PhobGCC/PhobGCC-SW/PhobGCC/common/stick.h

#ifndef STICKCAL_H
#define STICKCAL_H

#include <cmath>

#include "curveFitting.h"
#include "structsAndEnums.h"
#include "filter.h"

//TODO: either put these const globals in varables.h or make them #defines
//origin values, useful for writing readable stick positions
const int _intOrigin = 127;
const float _floatOrigin = 127.5;

//////values used for calibration
const int _noOfNotches = 16;
const int _noOfCalibrationPoints = _noOfNotches * 2;
const int _noOfAdjNotches = 12;
const int _fitOrder = 3; //fit order used in the linearization step
const float _maxStickAngle = 0.4886921906;//28 degrees; this is the max angular deflection of the stick.

const float _defaultCalPoints[_noOfCalibrationPoints] =  {
	0.0,0.0,//right
	0.0,0.0,
	0.0,0.0,//up right
	0.0,0.0,
	0.0,0.0,//up
	0.0,0.0,
	0.0,0.0,//up left
	0.0,0.0,
	0.0,0.0,//left
	0.0,0.0,
	0.0,0.0,//down left
	0.0,0.0,
	0.0,0.0,//down
	0.0,0.0,
	0.0,0.0,//down right
	0.0,0.0};

//Defaults
//                                                         right        notch 1      up right     notch 2      up           notch 3      up left      notch 4      left         notch 5      down left    notch 6      down         notch 7      down right   notch 8
//                                                         0            1            2            3            4            5            6            7            8            9            10           11           12           13           14           15
const int _calOrder[_noOfCalibrationPoints] =             {0, 1,        8, 9,       16, 17,       24, 25,      4, 5,        12, 13,      20, 21,      28, 29,      2, 3,        6, 7,        10, 11,      14, 15,      18, 19,      22, 23,      26, 27,      30, 31};
const float _notchAngleDefaults[_noOfNotches] =           {0,           M_PI/8.0,    M_PI*2/8.0,  M_PI*3/8.0,  M_PI*4/8.0,  M_PI*5/8.0,  M_PI*6/8.0,  M_PI*7/8.0,  M_PI*8/8.0,  M_PI*9/8.0,  M_PI*10/8.0, M_PI*11/8.0, M_PI*12/8.0, M_PI*13/8.0, M_PI*14/8.0, M_PI*15/8.0};
const NotchStatus _notchStatusDefaults[_noOfNotches] =    {CARDINAL,    TERT_ACTIVE, SECONDARY,   TERT_ACTIVE, CARDINAL,    TERT_ACTIVE, SECONDARY,   TERT_ACTIVE, CARDINAL,    TERT_ACTIVE, SECONDARY,   TERT_ACTIVE, CARDINAL,    TERT_ACTIVE, SECONDARY,   TERT_ACTIVE};
//                                                         up right     up left      down left    down right   notch 1      notch 2      notch 3      notch 4      notch 5      notch 6      notch 7      notch 8
const int _notchAdjOrder[_noOfAdjNotches] =               {2,           6,           10,          14,          1,           3,           5,           7,           9,           11,          13,          15};

float linearize(const float point, const float coefficients[]){
	return (coefficients[0]*(point*point*point) + coefficients[1]*(point*point) + coefficients[2]*point + coefficients[3]);
};

/*
 * calcStickValues computes the stick x/y coordinates from angle.
 * This requires weird trig because the stick moves spherically.
 */
void calcStickValues(float angle, float* x, float* y){
	*x = 100*atan2f((sinf(_maxStickAngle)*cosf(angle)),cosf(_maxStickAngle))/_maxStickAngle;
	*y = 100*atan2f((sinf(_maxStickAngle)*sinf(angle)),cosf(_maxStickAngle))/_maxStickAngle;
};

/*
 * Convert the x/y coordinates (actually angles on a sphere) to an azimuth
 * We first convert to a 3D coordinate and then drop to 2D, then arctan it
 * This does the opposite of calcStickValues, ideally.
 */
void angleOnSphere(const float x, const float y, float& angle){
	float xx = sinf(x*_maxStickAngle/100) * cosf(y*_maxStickAngle/100);
	float yy = cosf(x*_maxStickAngle/100) * sinf(y*_maxStickAngle/100);
	angle = atan2f(yy, xx);//WHY IS THIS BACKWARDS
	if(angle < 0){
		angle += 2*M_PI;
	}
};

/*
 * stripCalPoints removes the notches from un-cleaned cal points
 * this is so we can get the original values of the notches after the affine transform.
 * there need to be _noOfCalibrationPoints values in the inputs and outputs.
 */
void stripCalPoints(const float calPointsX[], const float calPointsY[], float strippedPointsX[], float strippedPointsY[]){
	for(int i=0; i < _noOfCalibrationPoints; i++){
		//start off by just copying them wholesale
		strippedPointsX[i] = calPointsX[i];
		strippedPointsY[i] = calPointsY[i];
		if((i+1)%4 == 0){//non-cardinal non-diagonal notch (every fourth starting at index 3)
			strippedPointsX[i] = calPointsX[0];//set equal to origin
			strippedPointsY[i] = calPointsY[0];
		}
	}
};

/*
 * computeStickAngles
 * write all the stick angles into the notch angles array array
 * inputs need to be length _noOfNotches+1
 * outputs need to be length _noOfNotches
 */
void computeStickAngles(float xInput[], float yInput[], float stickAngles[]){
	debug_println("Computed stick angles:");
	for(int i=0; i < _noOfNotches; i++){
		if(i%2 == 0){//cardinal or diagonal
			stickAngles[i] = _notchAngleDefaults[i];
		} else {
			angleOnSphere(xInput[i+1], yInput[i+1], stickAngles[i]);
		}
	}
};
//sets notches to measured values if absent
void cleanNotches(float notchAngles[], float measuredNotchAngles[], NotchStatus notchStatus[]){
	for(int i=0; i < _noOfNotches; i++){
		if(notchStatus[i] == TERT_INACTIVE){
			notchAngles[i] = measuredNotchAngles[i];
		}
	}
};

/*******************
	notchRemap
	Remaps the stick position using affine transforms generated from the notch positions
*******************/
void notchRemap(const float xIn, const float yIn, float* xOut, float* yOut, const int regions, const StickParams &stickParams, int currentCalStep, const ControlConfig &controls, const WhichStick whichStick){
	//determine the angle between the x unit vector and the current position vector
	float angle = atan2f(yIn,xIn);

	//unwrap the angle based on the first region boundary
	if(angle < stickParams.boundaryAngles[0]){
		angle += M_PI*2;
	}

	//go through the region boundaries from lowest angle to highest, checking if the current position vector is in that region
	//if the region is not found then it must be between the first and the last boundary, ie the last region
	//we check GATE_REGIONS*2 because each notch has its own very small region we use to make notch values more consistent
	//int region = regions*2-1;
	int region = regions-1;
	for(int i = 1; i < regions; i++){
		if(angle < stickParams.boundaryAngles[i]){
			region = i-1;
			break;
		}
	}

	//Apply the affine transformation using the coefficients found during calibration
	*xOut = stickParams.affineCoeffs[region][0]*xIn + stickParams.affineCoeffs[region][1]*yIn;
	*yOut = stickParams.affineCoeffs[region][2]*xIn + stickParams.affineCoeffs[region][3]*yIn;

	float stickScale;
	if(whichStick == ASTICK) {
		stickScale = controls.astickAnalogScaler/100.0f;
	} else {
		stickScale = controls.cstickAnalogScaler/100.0f;
	}

	*xOut *= stickScale;
	*yOut *= stickScale;

	if(currentCalStep == -1) {

		if(whichStick == ASTICK) {
			const int snapping = controls.astickCardinalSnapping;
			if(snapping > 0) {
				if((abs(*xOut)<snapping+0.5) && (abs(*yOut)>=79.5)){
					*xOut = 0;
				}
				if((abs(*yOut)<snapping+0.5) && (abs(*xOut)>=79.5)){
					*yOut = 0;
				}
			} else if(snapping < 0) {
				//Use this to prevent cardinals from ever being 1.0.
				//If you have it set to -1, it will prevent all 1.0 on vanilla and ucf prior to 0.84.
				//It will not prevent 1.0 on 'Melee 1.03'.
				//It will not prevent 1.0 on UCF 0.84, except for Zelda teleport (for some edge-cancel setups)
				//If you have it set to -2, it will prevent all 1.0 on vanilla and all UCF.
				//It will not prevent 1.0 on `Melee 1.03'.
				if((abs(*xOut) < ((snapping == -2) ? 6.5 : 0.5)) && (abs(*yOut)>=79.5)){
					if (*xOut >= 0) {
						*xOut = (snapping == -2) ? 7 : 1;
					} else {
						*xOut = (snapping == -2) ? -7 : -1;
					}
				}
				if((abs(*yOut) < ((snapping == -2) ? 6.5 : 0.5)) && (abs(*xOut)>=79.5)){
					if (*yOut >= 0) {
						*yOut = (snapping == -2) ? 7 : 1;
					} else {
						*yOut = (snapping == -2) ? -7 : -1;
					}
				}
			}
		} else {
			const int snapping = controls.cstickCardinalSnapping;
			if(snapping > 0) {
				if((abs(*xOut)<snapping+0.5) && (abs(*yOut)>=79.5)){
					*xOut = 0;
				}
				if((abs(*yOut)<snapping+0.5) && (abs(*xOut)>=79.5)){
					*yOut = 0;
				}
			} else if(snapping < 0) {
				if((abs(*xOut) < ((snapping == -2) ? 6.5 : 0.5)) && (abs(*yOut)>=79.5)){
					if (*xOut >= 0) {
						*xOut = (snapping == -2) ? 7 : 1;
					} else {
						*xOut = (snapping == -2) ? -7 : -1;
					}
				}
				if((abs(*yOut) < ((snapping == -2) ? 6.5 : 0.5)) && (abs(*xOut)>=79.5)){
					if (*yOut >= 0) {
						*yOut = (snapping == -2) ? 7 : 1;
					} else {
						*yOut = (snapping == -2) ? -7 : -1;
					}
				}
			}
		}

		if((abs(*xOut)<3) && (abs(*yOut)<3)) {
			*xOut = 0;
			*yOut = 0;
		}
	}
};

/*
 * transformCalPoints
 * remaps the cleaned calibration points from raw measurements to output coordinates
 * This seems redundant but we're feeding it coordinates without non-diagonal notches
 */
void transformCalPoints(const float xInput[], const float yInput[], float xOutput[], float yOutput[], const StickParams &stickParams, const ControlConfig &controls, const WhichStick whichStick){
	for(int i=0; i < _noOfNotches+1; i++){
		float xValue = linearize(xInput[i], stickParams.fitCoeffsX);
		float yValue = linearize(yInput[i], stickParams.fitCoeffsY);
		float outX;
		float outY;
		notchRemap(xValue, yValue, &outX, &outY, _noOfNotches, stickParams, 0, controls, whichStick);
		xOutput[i] = outX;
		yOutput[i] = outY;
	}
};

/*******************
	cleanCalPoints
	take the x and y coordinates and notch angles collected during the calibration procedure,
	and generate the cleaned (non-redundant) x and y stick coordinates and the corresponding x and y notch coordinates
*******************/
void cleanCalPoints(const float calPointsX[], const float calPointsY[], const float notchAngles[], float cleanedPointsX[], float cleanedPointsY[], float notchPointsX[], float notchPointsY[], NotchStatus notchStatus[]){

	debug_println("The raw calibration points (x,y) are:");
	for(int i = 0; i< _noOfCalibrationPoints; i++){
		debug_print(calPointsX[i], 4);
		debug_print(",");
		debug_println(calPointsY[i], 4);
	}

	debug_println("The notch angles are:");
	for(int i = 0; i< _noOfNotches; i++){
		debug_println(notchAngles[i], 4);
	}

	notchPointsX[0] = 0;
	notchPointsY[0] = 0;
	cleanedPointsX[0] = 0;
	cleanedPointsY[0] = 0;

	debug_println("The notch points are:");
	for(int i = 0; i < _noOfNotches; i++){
		//add the origin values to the first x,y point
		cleanedPointsX[0] += calPointsX[i*2];
		cleanedPointsY[0] += calPointsY[i*2];

		//copy the cal point into the cleaned list
		cleanedPointsX[i+1] = calPointsX[i*2+1];
		cleanedPointsY[i+1] = calPointsY[i*2+1];

		//convert notch angles to x/y coords (weird since the stick moves spherically)
		calcStickValues(notchAngles[i], notchPointsX+i+1, notchPointsY+i+1);
		notchPointsX[i+1] = round(notchPointsX[i+1]);
		notchPointsY[i+1] = round(notchPointsY[i+1]);

		debug_print(notchPointsX[i+1]);
		debug_print(",");
		debug_println(notchPointsY[i+1]);
	}

	//remove the largest and smallest two origin values to remove outliers
	//first, find their indices
	int smallestX = 0;
	int smallX = 0;
	int largeX = 0;
	int largestX = 0;
	int smallestY = 0;
	int smallY = 0;
	int largeY = 0;
	int largestY = 0;
	for (int i = 0; i < _noOfNotches; i++){
		if (calPointsX[i*2] < calPointsX[smallestX]){//if it's the new smallest
			smallX = smallestX;//shuffle the old smallest to small
			smallestX = i*2;//record the new smallest index
		} else if (calPointsX[i*2] < calPointsX[smallX]){//if it's the new second-smallest
			smallX = i*2;//record the new small index
		}
		if (calPointsX[i*2] > calPointsX[largestX]){//if it's the new largest
			largeX = largestX;//shuffle the old largest to large
			largestX = i*2;//record the new largest index
		} else if (calPointsX[i*2] > calPointsX[largeX]){//if it's the new second-largest
			largeX = i*2;//record the new large index
		}
		if (calPointsY[i*2] < calPointsY[smallestY]){
			smallY = smallestY;
			smallestY = i*2;
		} else if (calPointsY[i*2] < calPointsY[smallY]){
			smallY = i*2;
		}
		if (calPointsY[i*2] > calPointsY[largestY]){
			largeY = largestY;
			largestY = i*2;
		} else if (calPointsY[i*2] > calPointsY[largeY]){
			largeY = i*2;
		}
	}
	//subtract the smallest and largest values
	cleanedPointsX[0] -= calPointsX[smallestX];
	cleanedPointsX[0] -= calPointsX[smallX];
	cleanedPointsX[0] -= calPointsX[largeX];
	cleanedPointsX[0] -= calPointsX[largestX];
	cleanedPointsY[0] -= calPointsY[smallestY];
	cleanedPointsY[0] -= calPointsY[smallY];
	cleanedPointsY[0] -= calPointsY[largeY];
	cleanedPointsY[0] -= calPointsY[largestY];

	//divide by the total number of calibration steps/2 to get the average origin value
	//except it's minus 4 steps since we removed outliers
	cleanedPointsX[0] = cleanedPointsX[0]/((float)_noOfNotches-4);
	cleanedPointsY[0] = cleanedPointsY[0]/((float)_noOfNotches-4);

	for(int i = 0; i < _noOfNotches; i++){
		//calculate radius of cleaned point from center
		float deltaX = cleanedPointsX[i+1] - cleanedPointsX[0];
		float deltaY = cleanedPointsY[i+1] - cleanedPointsY[0];
		float mag = sqrt(deltaX*deltaX + deltaY*deltaY);

		if(mag < 0.02 && (i%2) != 0){//if the cleaned point was at the center and would be a firefox notch
			//average the previous and next points (cardinal & diagonal) for some sanity
			int prevIndex = ((i-1+_noOfNotches) % _noOfNotches) + 1;
			int nextIndex = ((i+1) % _noOfNotches) + 1;

			cleanedPointsX[i+1] = (cleanedPointsX[prevIndex] + cleanedPointsX[nextIndex])/2.0;
			cleanedPointsY[i+1] = (cleanedPointsY[prevIndex] + cleanedPointsY[nextIndex])/2.0;

			notchPointsX[i+1] = (notchPointsX[prevIndex] + notchPointsX[nextIndex])/2.0;
			notchPointsY[i+1] = (notchPointsY[prevIndex] + notchPointsY[nextIndex])/2.0;

			debug_print("no input was found for notch: ");
			debug_println(i+1);

			//Mark that notch adjustment should be skipped for this
			notchStatus[i] = TERT_INACTIVE;
		}else{
			notchStatus[i] = _notchStatusDefaults[i];
		}
	}

	debug_println("The cleaned calibration points are:");
	for(int i = 0; i< (_noOfNotches+1); i++){
		debug_print(cleanedPointsX[i], 4);
		debug_print(",");
		debug_println(cleanedPointsY[i], 4);
	}

	debug_println("The corresponding notch points are:");
	for(int i = 0; i< (_noOfNotches+1); i++){
		debug_print(notchPointsX[i]);
		debug_print(",");
		debug_println(notchPointsY[i]);
	}

	debug_println("The notch statuses are:");
	for(int i = 0; i< (_noOfNotches); i++){
		debug_println(notchStatus[i]);
	}
};

//The notch adjustment is limited in order to control
//1. displacement of points (max 12 units out of +/- 100, for now)
//2. stretching of coordinates (max +/- 30%)
void legalizeNotch(const int notchIndex, float measuredNotchAngles[], float notchAngles[], NotchStatus notchStatus[]){
	//Limit the notch adjustment

	//Start out with the limits being 12 units around the circle at the gate
	/*this may be unnecessary in our case, because 12 units is also the 30% stretch limit
	float lowerPosLimit = measuredNotchAngles[notchIndex] - 12/100.f;
	float upperPosLimit = measuredNotchAngles[notchIndex] + 12/100.f;
	if(upperPosLimit < lowerPosLimit){
		upperPosLimit += 2*M_PI;
	}
	*/

	bool isDiagonal = false;

	//Now we need to determine the stretch/compression limit
	//Figure out the previous and next notch angles.
	//For most they're the adjacent notches.
	int prevIndex = (notchIndex-1+_noOfNotches) % _noOfNotches;
	int nextIndex = (notchIndex+1) % _noOfNotches;
	//For diagonals, the cardinals are the index points.
	if((notchIndex - 2) % 4 == 0){
		prevIndex = (notchIndex-2+_noOfNotches) % _noOfNotches;
		nextIndex = (notchIndex+2) % _noOfNotches;
		isDiagonal = true;
	}
	float prevAngle = notchAngles[prevIndex];
	float nextAngle = notchAngles[nextIndex];
	if(nextAngle < prevAngle){
		nextAngle += 2*M_PI;
	}
	float prevMeasAngle = measuredNotchAngles[prevIndex];
	float thisMeasAngle = measuredNotchAngles[notchIndex];
	float nextMeasAngle = measuredNotchAngles[nextIndex];
	if(nextMeasAngle < thisMeasAngle){
		nextMeasAngle += 2*M_PI;
	}

	float cmpAmt;
	float strAmt;
	if(isDiagonal) {//tighter bounds for diagonals
		cmpAmt = 0.769;
		strAmt = 1.3;
	} else {//wider bounds for modder notches
		cmpAmt = 0.5;
		strAmt = 2.0;
	}

	float lowerCompressLimit = prevAngle + cmpAmt*(thisMeasAngle-prevMeasAngle);//how far we can squish when reducing the angle
	float lowerStretchLimit  = nextAngle - strAmt*(nextMeasAngle-thisMeasAngle);//how far we can stretch when reducing the angle
	float upperCompressLimit = nextAngle - cmpAmt*(nextMeasAngle-thisMeasAngle);//how far we can squish when increasing the angle
	float upperStretchLimit  = prevAngle + strAmt*(thisMeasAngle-prevMeasAngle);//how far we can stretch when increasing the angle

	//Now, in order to apply stretch leniency to angles within the deadzone,
	// we need to figure out whether the previous angle or next angle was a cardinal.
	//If the previous one is a cardinal AND the angle is in the deadzone, we make the upperstretchlimit bigger, only if it can't reach 0.3000.
	const float minThreshold  = 0.1500/0.9750;//radians; we don't want to fix things smaller than this
	const float deadzoneLimit = 0.2875/0.9500;//radians; or things larger than this
	const float deadzonePlus  = 0.3250/0.9375;//radians; we want to make sure the adjustment can make it here
	if(prevIndex % 4 == 0 && !isDiagonal && (thisMeasAngle-prevMeasAngle) > minThreshold && (thisMeasAngle-prevMeasAngle) < deadzoneLimit){
		upperStretchLimit = prevAngle + fmax(strAmt*(thisMeasAngle-prevMeasAngle), deadzonePlus);
	}
	//If the next one is a cardinal AND the angle is in the deadzone, we make the lowerstretchlimit smaller.
	if(nextIndex % 4 == 0 && !isDiagonal && (nextMeasAngle-thisMeasAngle) > minThreshold && (nextMeasAngle-thisMeasAngle) < deadzoneLimit){
		lowerStretchLimit = nextAngle - fmax(strAmt*(nextMeasAngle-thisMeasAngle), deadzonePlus);
	}

	float lowerDistortLimit  = fmax(lowerCompressLimit, lowerStretchLimit);
	float upperDistortLimit  = fmin(upperCompressLimit, upperStretchLimit);
	if(upperDistortLimit < lowerDistortLimit){
		upperDistortLimit += 2*M_PI;
	}

	//Combine the limits
	float lowerLimit = lowerDistortLimit;//fmax(lowerStretchLimit, lowerPosLimit);
	float upperLimit = upperDistortLimit;//fmin(upperStretchLimit, upperPosLimit);
	if(upperLimit < lowerLimit){
		upperLimit += 2*M_PI;
	}

	//Apply the limits
	notchAngles[notchIndex] = fmax(notchAngles[notchIndex], lowerLimit);
	notchAngles[notchIndex] = fmin(notchAngles[notchIndex], upperLimit);
}

void legalizeNotches(const int currentStepIn, float measuredNotchAngles[], float notchAngles[], NotchStatus notchStatus[]){
	for(int i=currentStepIn; i < 44; i++) {
		const int notchIndex = _notchAdjOrder[i-_noOfCalibrationPoints];
		legalizeNotch(notchIndex, measuredNotchAngles, notchAngles, notchStatus);
	}
}

//adjustNotch is used to adjust the angles of the notch.
//It is run after calibration points are collected.
//It runs a legalization routine to limit subsequent notches
void adjustNotch(const int currentStepIn, const float loopDelta, const WhichStick whichStick, float measuredNotchAngles[], float notchAngles[], NotchStatus notchStatus[], Buttons &btn, Buttons &hardware){
	//set up variables based on current button state
	bool CW = hardware.X;
	bool CCW = hardware.Y;
	bool reset = btn.B;

	//This gets run after all the calibration points are collected
	//So we subtract the number of calibration points and switch over to notch adjust order
	const int notchIndex = _notchAdjOrder[currentStepIn-_noOfCalibrationPoints];

	//display the desired value on the other stick
	float x = 0;
	float y = 0;
	calcStickValues(measuredNotchAngles[notchIndex], &x, &y);
	if(whichStick == ASTICK){
		btn.Cx = (uint8_t) (x + _floatOrigin);
		btn.Cy = (uint8_t) (y + _floatOrigin);
	} else {
		btn.Ax = (uint8_t) (x + _floatOrigin);
		btn.Ay = (uint8_t) (y + _floatOrigin);
	}

	//do nothing if it's not a valid notch to calibrate
	//it'll skip them anyway but just in case
	if(notchStatus[notchIndex] == TERT_INACTIVE){
		return;
	}

	//Adjust notch angle according to which button is pressed (do nothing for both buttons)
	if(CW && !CCW){
		notchAngles[notchIndex] -= loopDelta*0.000075;
	} else if(CCW && !CW){
		notchAngles[notchIndex] += loopDelta*0.000075;
	} else if(reset){
		notchAngles[notchIndex] = measuredNotchAngles[notchIndex];
	} else {
		return;
	}

	legalizeNotches(currentStepIn, measuredNotchAngles, notchAngles, notchStatus);
	//legalizeNotch(notchIndex, measuredNotchAngles, notchAngles, notchStatus);
};

//displayNotch is used in lieu of adjustNotch when doing basic calibration
void displayNotch(const int currentStepIn, const bool calibratingAStick, const float notchAngles[], Buttons &btn){
	int currentStep = _calOrder[currentStepIn];
	//display the desired value on the other stick
	float x = 0;
	float y = 0;
	if(currentStep%2){
		const int notchIndex = currentStep/2;
		calcStickValues(notchAngles[notchIndex], &x, &y);
	}
	if(calibratingAStick){
		btn.Cx = (uint8_t) (x + _floatOrigin);
		btn.Cy = (uint8_t) (y + _floatOrigin);
	}else{
		btn.Ax = (uint8_t) (x + _floatOrigin);
		btn.Ay = (uint8_t) (y + _floatOrigin);
	}
};

void insertCalPoints(const WhichStick whichStick, const int currentStepIn, float calPointsX[], float calPointsY[], Pins &pin, float X, float Y){
	debug_print("Inserting cal point for step: ");
	debug_println(currentStepIn);
    const int currentStep = _calOrder[currentStepIn];

	debug_print("Cal point number: ");
	debug_println(currentStep);

	calPointsX[currentStep] = X;
	calPointsY[currentStep] = Y;

	debug_println("The collected coordinates are: ");
	debug_println(calPointsX[currentStep],8);
	debug_println(calPointsY[currentStep],8);
};

/*******************
	linearizeCal
	Generate a fit to linearize the stick response.
	Inputs:
		cleaned points X and Y, (must be 17 points for each of these, the first being the center, the others starting at 3 oclock and going around counterclockwise)
	Outputs:
		linearization fit coefficients for X and Y
*******************/
void linearizeCal(const float inX[], const float inY[], float outX[], float outY[], StickParams &stickParams){
	//if the fit points are 0, then output 0 fit parameters
	if((inX[0] == 0) && (inY[0] == 0)) {
		outX[0] = 0;
		outX[1] = 0;
		outX[3] = 0;
		outX[4] = 0;
		outX[5] = 0;
		outY[0] = 0;
		outY[1] = 0;
		outY[3] = 0;
		outY[4] = 0;
		outY[5] = 0;
		return;
	}
	debug_println("beginning linearization");

	//do the curve fit first
	//generate all the notched/not notched specific cstick values we will need

	double fitPointsX[5];
	double fitPointsY[5];

	fitPointsX[0] = inX[8+1];                   //right
	fitPointsX[1] = (inX[6+1] + inX[10+1])/2.0; //right 45 deg
	fitPointsX[2] = inX[0];                     //center
	fitPointsX[3] = (inX[2+1] + inX[14+1])/2.0; //left 45 deg
	fitPointsX[4] = inX[0+1];                   //left

	fitPointsY[0] = inY[12+1];                  //down
	fitPointsY[1] = (inY[10+1] + inY[14+1])/2.0;//down 45 deg
	fitPointsY[2] = inY[0];                     //center
	fitPointsY[3] = (inY[6+1] + inY[2+1])/2.0;  //up 45 deg
	fitPointsY[4] = inY[4+1];                   //up


	//////determine the coefficients needed to linearize the stick
	//create the expected output, what we want our curve to be fit too
	//this is hard coded because it doesn't depend on the notch adjustments
	//                   -100 -74.246        0     74.246         100, centered around 0-255
    //It's not sin(45 deg) because it's a spherical motion, not planar.
	double x_output[5] = {27.5,53.2537879754,127.5,201.7462120246,227.5};
	double y_output[5] = {27.5,53.2537879754,127.5,201.7462120246,227.5};

	debug_println("The fit input points are (x,y):");
	for(int i = 0; i < 5; i++){
		debug_print(fitPointsX[i],8);
		debug_print(",");
		debug_println(fitPointsY[i],8);
	}

	debug_println("The corresponding fit output points are (x,y):");
	for(int i = 0; i < 5; i++){
		debug_print(x_output[i]);
		debug_print(",");
		debug_println(y_output[i]);
	}

	//perform the curve fit, order is 3
	double tempCoeffsX[_fitOrder+1];
	double tempCoeffsY[_fitOrder+1];

	fitCurve(_fitOrder, 5, fitPointsX, x_output, _fitOrder+1, tempCoeffsX);
	fitCurve(_fitOrder, 5, fitPointsY, y_output, _fitOrder+1, tempCoeffsY);

	//write these coefficients to the array that was passed in, this is our first output
	for(int i = 0; i < (_fitOrder+1); i++){
		stickParams.fitCoeffsX[i] = tempCoeffsX[i];
		stickParams.fitCoeffsY[i] = tempCoeffsY[i];
	}

	//we will now take out the offset, making the range -100 to 100 instead of 28 to 228
	//calculate the offset
	float xZeroError = linearize((float)fitPointsX[2], stickParams.fitCoeffsX);
	float yZeroError = linearize((float)fitPointsY[2], stickParams.fitCoeffsY);

	//Adjust the fit's constant coefficient so that the stick zero position is 0
	stickParams.fitCoeffsX[3] = stickParams.fitCoeffsX[3] - xZeroError;
	stickParams.fitCoeffsY[3] = stickParams.fitCoeffsY[3] - yZeroError;

	debug_println("The fit coefficients are  are (x,y):");
	for(int i = 0; i < 4; i++){
		debug_print(stickParams.fitCoeffsX[i]);
		debug_print(",");
		debug_println(stickParams.fitCoeffsY[i]);
	}

	debug_println("The linearized points are:");
	for(int i = 0; i <= _noOfNotches; i++){
		outX[i] = linearize(inX[i], stickParams.fitCoeffsX);
		outY[i] = linearize(inY[i], stickParams.fitCoeffsY);
		debug_print(outX[i],8);
		debug_print(",");
		debug_println(outY[i],8);
	}
};

//Self-explanatory.
void inverse(const float in[3][3], float (&out)[3][3])
{
	float det = in[0][0] * (in[1][1]*in[2][2] - in[2][1]*in[1][2]) -
	            in[0][1] * (in[1][0]*in[2][2] - in[1][2]*in[2][0]) +
	            in[0][2] * (in[1][0]*in[2][1] - in[1][1]*in[2][0]);
	float invdet = 1 / det;

	out[0][0] = (in[1][1]*in[2][2] - in[2][1]*in[1][2]) * invdet;
	out[0][1] = (in[0][2]*in[2][1] - in[0][1]*in[2][2]) * invdet;
	out[0][2] = (in[0][1]*in[1][2] - in[0][2]*in[1][1]) * invdet;
	out[1][0] = (in[1][2]*in[2][0] - in[1][0]*in[2][2]) * invdet;
	out[1][1] = (in[0][0]*in[2][2] - in[0][2]*in[2][0]) * invdet;
	out[1][2] = (in[1][0]*in[0][2] - in[0][0]*in[1][2]) * invdet;
	out[2][0] = (in[1][0]*in[2][1] - in[2][0]*in[1][1]) * invdet;
	out[2][1] = (in[2][0]*in[0][1] - in[0][0]*in[2][1]) * invdet;
	out[2][2] = (in[0][0]*in[1][1] - in[1][0]*in[0][1]) * invdet;
}

//Self-explanatory.
void matrixMatrixMult(const float left[3][3], const float right[3][3], float (&output)[3][3])
{
	for (int i = 0; i < 3; i++)
	{
		for (int j = 0; j < 3; j++)
		{
			output[i][j] = 0;
			for (int k = 0; k < 3; k++)
			{
				output[i][j] += left[i][k] * right[k][j];
			}
		}
	}
}

void print_mtx(const float matrix[3][3]){
	int i, j, nrow, ncol;
	nrow = 3;
	ncol = 3;
	debug_println();
	for (i=0; i<nrow; i++)
	{
		for (j=0; j<ncol; j++)
		{
			debug_print(matrix[i][j], 6);   // print 6 decimal places
			debug_print(", ");
		}
		debug_println();
	}
	debug_println();
};


void notchCalibrate(const float xIn[], const float yIn[], const float xOut[], const float yOut[], const int regions, StickParams &stickParams){
	for(int i = 1; i <= regions; i++){
		debug_print("calibrating region: ");
		debug_println(i);

		float pointsIn[3][3];
		float pointsOut[3][3];

		if(i == (regions)){
			debug_println("final region");
			pointsIn[0][0] = xIn[0];
			pointsIn[0][1] = xIn[i];
			pointsIn[0][2] = xIn[1];
			pointsIn[1][0] = yIn[0];
			pointsIn[1][1] = yIn[i];
			pointsIn[1][2] = yIn[1];
			pointsIn[2][0] = 1;
			pointsIn[2][1] = 1;
			pointsIn[2][2] = 1;
			pointsOut[0][0] = xOut[0];
			pointsOut[0][1] = xOut[i];
			pointsOut[0][2] = xOut[1];
			pointsOut[1][0] = yOut[0];
			pointsOut[1][1] = yOut[i];
			pointsOut[1][2] = yOut[1];
			pointsOut[2][0] = 1;
			pointsOut[2][1] = 1;
			pointsOut[2][2] = 1;
		}
		else{
			pointsIn[0][0] = xIn[0];
			pointsIn[0][1] = xIn[i];
			pointsIn[0][2] = xIn[i+1];
			pointsIn[1][0] = yIn[0];
			pointsIn[1][1] = yIn[i];
			pointsIn[1][2] = yIn[i+1];
			pointsIn[2][0] = 1;
			pointsIn[2][1] = 1;
			pointsIn[2][2] = 1;
			pointsOut[0][0] = xOut[0];
			pointsOut[0][1] = xOut[i];
			pointsOut[0][2] = xOut[i+1];
			pointsOut[1][0] = yOut[0];
			pointsOut[1][1] = yOut[i];
			pointsOut[1][2] = yOut[i+1];
			pointsOut[2][0] = 1;
			pointsOut[2][1] = 1;
			pointsOut[2][2] = 1;
		}

		debug_println("In points:");
		print_mtx(pointsIn);
		debug_println("Out points:");
		print_mtx(pointsOut);

		float temp[3][3];
		inverse(pointsIn, temp);

		float A[3][3];
		matrixMatrixMult(pointsOut, temp, A);

		debug_println("The transform matrix is:");
		print_mtx(A);

		debug_println("The affine transform coefficients for this region are:");

		for(int j = 0; j <2;j++){
			for(int k = 0; k<2;k++){
				stickParams.affineCoeffs[i-1][j*2+k] = A[j][k];
				debug_print(stickParams.affineCoeffs[i-1][j*2+k]);
				debug_print(",");
			}
		}

		debug_println();
		debug_println("The angle defining this  regions is:");
		stickParams.boundaryAngles[i-1] = atan2f((yIn[i]-yIn[0]),(xIn[i]-xIn[0]));
		//unwrap the angles so that the first has the smallest value
		if(stickParams.boundaryAngles[i-1] < stickParams.boundaryAngles[0]){
			stickParams.boundaryAngles[i-1] += M_PI*2;
		}
		debug_println(stickParams.boundaryAngles[i-1]);
	}
};

#endif //STICKCAL_H
