PhobGCC/PhobGCC-SW/PhobGCC/rp2040/src/navigateMenu.cpp

#include <cmath>
#include "pico.h"
#include "hardware/timer.h"
#include "cvideo.h"
#include "menu.h"
#include "menuStrings.h"
#include "storage/pages/storage.h"

#define APRESS  0b0000'0000'0000'0001
#define BSAVE   0b0000'0000'0000'0010
#define BPRESS  0b0000'0000'0000'0100
#define DUPRESS 0b0000'0000'0000'1000
#define DDPRESS 0b0000'0000'0001'0000
#define DLPRESS 0b0000'0000'0010'0000
#define DRPRESS 0b0000'0000'0100'0000
#define LRPRESS 0b0000'0000'1000'0000
#define XPRESS  0b0000'0001'0000'0000
#define YPRESS  0b0000'0010'0000'0000
#define ZPRESS  0b0000'0100'0000'0000
#define SPRESS  0b0000'1000'0000'0000
#define BTAP    0b0001'0000'0000'0000

void navigateMenu(unsigned char bitmap[],
		unsigned int &menu,
		int &itemIndex,
		uint8_t &redraw,
		bool &changeMade,
		const int currentCalStep,
		const int currentRemapStep,
		volatile uint8_t &pleaseCommit,
		const Buttons &btn,
		uint16_t presses,
		ControlConfig &controls,
		DataCapture &capture);

void __time_critical_func(handleMenuButtons)(unsigned char bitmap[],
		unsigned int &menu,
		int &itemIndex,
		uint8_t &redraw,
		bool &changeMade,
		const int currentCalStep,
		const int currentRemapStep,
		volatile uint8_t &pleaseCommit,
		const Buttons &btn,
		const Buttons &hardware,
		ControlConfig &controls,
		DataCapture &capture) {
	uint16_t presses = 0;

	//b button needs to accumulate before acting
	static uint8_t backAccumulator = 0;
	//a and dpad are locked out after acting
	const uint8_t buttonLockout = 6;// 1/10 of a second of ignoring button bounce
	const uint8_t dpadLockout = 15;// 1/4 of a second of ignoring button bounce
	const uint8_t dpadLockoutShort = 3;// 1/20 of a second of ignoring button bounce
	static uint8_t aLockout = 0;
	static uint8_t zLockout = 0;
	static uint8_t sLockout = 0;
	static uint8_t lrLockout = 0;
	static uint8_t duLockout = 0;
	static uint8_t ddLockout = 0;
	static uint8_t dlLockout = 0;
	static uint8_t drLockout = 0;
	//only decrement the lockout if the button/direction is released so it doesn't repeat
	//it'll be unlocked after it hits zero
	if(!hardware.A && aLockout > 0) {
		aLockout--;
	}
	if(!hardware.L && !hardware.R && lrLockout > 0) {
		lrLockout--;
	}
	if(!hardware.Z && zLockout > 0) {
		zLockout--;
	}
	if(!hardware.S && sLockout > 0) {
		sLockout--;
	}
	//dpad directions do repeat
	duLockout = fmax(0, duLockout - 1);
	ddLockout = fmax(0, ddLockout - 1);
	dlLockout = fmax(0, dlLockout - 1);
	drLockout = fmax(0, drLockout - 1);

	static uint8_t duCounter = 0;//for controls that go faster when you hold them
	static uint8_t ddCounter = 0;//for controls that go faster when you hold them
	static uint8_t dlCounter = 0;//for controls that go faster when you hold them
	static uint8_t drCounter = 0;//for controls that go faster when you hold them

	if(hardware.B) {
		presses = presses | BTAP;
		backAccumulator++;
		if(backAccumulator == 5) {//only call save once per 0.5 second B hold
			presses = presses | BSAVE;
		}
		if(backAccumulator >= 30) {
			backAccumulator = 0;
			aLockout = 0;//make A available immediately after backing out
			presses = presses | BPRESS;
			capture.autoRepeat = false;//cancel auto repeating if you back out
			capture.begin = false;
			capture.triggered = false;
			capture.done = true;
			pleaseCommit = 0;
		}
	} else {
		if(backAccumulator > 0) {
			backAccumulator--;
		}
		if(hardware.A && aLockout == 0) {
			presses = presses | APRESS;
			aLockout = buttonLockout;
		} else if(hardware.Z && zLockout == 0) {
			presses = presses | ZPRESS;
			zLockout = buttonLockout;
		} else if(hardware.S && sLockout == 0) {
			presses = presses | SPRESS;
			sLockout = buttonLockout;
		} else if((hardware.L || hardware.R) && lrLockout == 0) {
			presses = presses | LRPRESS;
			lrLockout = buttonLockout;
		} else if(hardware.Dl && dlLockout == 0) {
			presses = presses | DLPRESS;
			//Go faster after 10 steps
			if(dlCounter <= 10) {
				dlCounter++;
			}
			drCounter = 0;
			dlLockout = dlCounter > 10 ? dpadLockoutShort : dpadLockout;
			drLockout = 0;
			//also lock out perpendicular directions to prevent misinputs
			ddLockout = dpadLockout;
			duLockout = dpadLockout;
			//clear the perpendicular repetition counters
			duCounter = 0;
			ddCounter = 0;
		} else if(hardware.Dr && drLockout == 0) {
			presses = presses | DRPRESS;
			//Go faster after 10 steps
			if(drCounter <= 10) {
				drCounter++;
			}
			drLockout = drCounter > 10 ? dpadLockoutShort : dpadLockout;
			dlLockout = 0;
			//also lock out perpendicular directions to prevent misinputs
			ddLockout = dpadLockout;
			duLockout = dpadLockout;
			//clear the perpendicular repetition counters
			duCounter = 0;
			ddCounter = 0;
		} else if(hardware.Du && duLockout == 0) {
			presses = presses | DUPRESS;
			//Go faster after 10 steps
			if(duCounter <= 10) {
				duCounter++;
			}
			ddCounter = 0;
			duLockout = duCounter > 10 ? dpadLockoutShort : dpadLockout;
			ddLockout = 0;
			//also lock out perpendicular directions to prevent misinputs
			dlLockout = dpadLockout;
			drLockout = dpadLockout;
			//clear the perpendicular repetition counters
			dlCounter = 0;
			drCounter = 0;
		} else if(hardware.Dd && ddLockout == 0) {
			presses = presses | DDPRESS;
			//Go faster after 10 steps
			if(ddCounter <= 10) {
				ddCounter++;
			}
			duCounter = 0;
			ddLockout = ddCounter > 10 ? dpadLockoutShort : dpadLockout;
			duLockout = 0;
			//also lock out perpendicular directions to prevent misinputs
			dlLockout = dpadLockout;
			drLockout = dpadLockout;
			//clear the perpendicular repetition counters
			dlCounter = 0;
			drCounter = 0;
		} else {
			//clear the repetition counters
			if(duLockout == 0) {
				duCounter = 0;
			}
			if(ddLockout == 0) {
				ddCounter = 0;
			}
			if(dlLockout == 0) {
				dlCounter = 0;
			}
			if(drLockout == 0) {
				drCounter = 0;
			}
		}
		//Other presses that don't get locked out, not for navigation
		if(hardware.X) {
			presses = presses | XPRESS;
		}
		if(hardware.Y) {
			presses = presses | YPRESS;
		}
	}

	//handle autorepeat
	if(capture.autoRepeat && capture.done) {
		const uint8_t repeatTimerDuration = 15;
		static uint8_t repeatTimer = repeatTimerDuration;
		if(repeatTimer == 0) {
			presses = SPRESS;//ignore other things, just make it press start
			repeatTimer = repeatTimerDuration;
		} else {
			repeatTimer--;
		}
	}

	//handle a game returning
	if(pleaseCommit == 99) {
		//behave like a long B press, because that's what happened in game
		backAccumulator = 0;
		aLockout = 0;//make A available immediately after backing out
		presses = presses | BPRESS;
		capture.autoRepeat = false;//cancel auto repeating if you back out
		capture.begin = false;
		capture.triggered = false;
		capture.done = true;
		pleaseCommit = 0;
	}

	//handle actual navigation and settings changes
	if(presses) {
		navigateMenu(bitmap,
				menu,
				itemIndex,
				redraw,
				changeMade,
				currentCalStep,
				currentRemapStep,
				pleaseCommit,
				btn,
				presses,
				controls,
				capture);
	}
	//handle always-redrawing screens since we don't always call navigation
	//redraw = 2 asks for a fast-path
	if(redraw == 0) {
		if(menu == MENU_STICKDBG && itemIndex == 0) {
			redraw = 2;
		} else if(menu == MENU_TRIGGER || menu == MENU_LTRIGGER || menu == MENU_RTRIGGER) {
			redraw = 2;
		} else if(menu == MENU_ASTICKCAL || menu == MENU_CSTICKCAL) {
			redraw = 2;
		} else if(menu == MENU_INPUTVIEW) {
			redraw = 2;
		}
	}
}

void navigateMenu(unsigned char bitmap[],
		unsigned int &menu,
		int &itemIndex,
		uint8_t &redraw,
		bool &changeMade,
		const int currentCalStep,
		const int currentRemapStep,
		volatile uint8_t &pleaseCommit,
		const Buttons &btn,
		uint16_t presses,
		ControlConfig &controls,
		DataCapture &capture) {

	//store previous menu positions
	static bool itemIndexInitialized = false;
	static uint8_t itemIndexList[MENUCOUNT];
	if(!itemIndexInitialized) {
		for(int i = 0; i < MENUCOUNT; i++) {
			itemIndexList[i] = 0;
		}
		itemIndexInitialized = true;
	}


	if(MenuIndex[menu][1] == 0) {
		if(presses & APRESS) {
			presses = 0;
			itemIndexList[menu] = itemIndex;
			menu = MenuIndex[menu][2];
			itemIndex = itemIndexList[menu];
			redraw = 1;
		}
	} else if(MenuIndex[menu][1] > 0) {
		//handle holding the B button as long as you're not on the splashscreen or calibrating or remapping
		if(presses & BPRESS) {
			if(((menu == MENU_ASTICKCAL || menu == MENU_CSTICKCAL) && (currentCalStep >= 0)) || (menu == MENU_REMAP && currentRemapStep >= 0)) {
				//do nothing
			} else {
				presses = 0;
				itemIndexList[menu] = itemIndex;
				menu = MenuIndex[menu][0];
				itemIndex = itemIndexList[menu];
				changeMade = false;
				redraw = 1;
			}
		}
		if(MenuIndex[menu][1] <= 6) {
			//if it's a submenu, handle a, dup, and ddown
			if(presses & APRESS) {
				presses = 0;
				itemIndexList[menu] = itemIndex;
				menu = MenuIndex[menu][itemIndex + 2];
				itemIndex = itemIndexList[menu];
				changeMade = false;
				redraw = 1;
				//don't return, we may want to handle setup things below
			} else if(presses & DUPRESS) {
				presses = 0;
				itemIndex = fmax(0, itemIndex-1);
				redraw = 1;
				return;
			} else if(presses & DDPRESS) {
				presses = 0;
				itemIndex = fmin(MenuIndex[menu][1]-1, itemIndex+1);
				redraw = 1;
			}
		}
		//Big switch case for controls for all the bottom level items
		static int tempInt1 = 0;
		static int tempInt2 = 0;
		static int tempInt3 = 0;
		switch(menu) {
			case MENU_ASTICKCAL:
				if(presses & (APRESS | LRPRESS)) {
					pleaseCommit = 4;
				} else if(presses & SPRESS) {
					pleaseCommit = 7;
				} else if(presses & ZPRESS) {
					pleaseCommit = 6;
				}
				return;
			case MENU_CSTICKCAL:
				if(presses & (APRESS | LRPRESS)) {
					pleaseCommit = 5;
				} else if(presses & SPRESS) {
					pleaseCommit = 7;
				} else if(presses & ZPRESS) {
					pleaseCommit = 6;
				}
				return;
			case MENU_AUTOINIT:
				if(!changeMade) {
					tempInt1 = controls.autoInit;
				}
				if(presses & DUPRESS) {
					controls.autoInit = true;
					changeMade = controls.autoInit != tempInt1;
					redraw = 1;
				} else if(presses & DDPRESS) {
					controls.autoInit = false;
					changeMade = controls.autoInit != tempInt1;
					redraw = 1;
				} else if((presses & BSAVE) && changeMade) {
					setAutoInitSetting(controls.autoInit);
					tempInt1 = controls.autoInit;
					changeMade = false;
					redraw = 1;
					pleaseCommit = 1;//ask the other thread to commit settings to flash
				}
				return;
			case MENU_STICKDBG:
				//A cycles through pages
				if(presses & APRESS) {
					itemIndex++;
					if(itemIndex > 3) {
						itemIndex = 0;
					}
					redraw = 1;
				}
				return;
			case MENU_ASNAPBACK:
				if(!changeMade) {
					tempInt1 = controls.xSnapback;
					tempInt2 = controls.ySnapback;
				}
				if(presses & DLPRESS) {
					itemIndex = 0;
					redraw = 1;
				} else if(presses & DRPRESS) {
					itemIndex = 1;
					redraw = 1;
				} else if(presses & DUPRESS) {
					if(itemIndex == 0) {
						controls.xSnapback = fmin(controls.snapbackMax, controls.xSnapback+1);
					} else {//itemIndex == 1
						controls.ySnapback = fmin(controls.snapbackMax, controls.ySnapback+1);
					}
					changeMade = (controls.xSnapback != tempInt1) || (controls.ySnapback != tempInt2);
					redraw = 1;
				} else if(presses & DDPRESS) {
					if(itemIndex == 0) {
						controls.xSnapback = fmax(controls.snapbackMin, controls.xSnapback-1);
					} else {//itemIndex == 1
						controls.ySnapback = fmax(controls.snapbackMin, controls.ySnapback-1);
					}
					changeMade = (controls.xSnapback != tempInt1) || (controls.ySnapback != tempInt2);
					redraw = 1;
				} else if((presses & BSAVE) && changeMade) {
					setXSnapbackSetting(controls.xSnapback);
					setYSnapbackSetting(controls.ySnapback);
					tempInt1 = controls.xSnapback;
					tempInt2 = controls.ySnapback;
					changeMade = false;
					redraw = 1;
					pleaseCommit = 1;//ask the other thread to commit settings to flash
				}
				return;
			case MENU_AWAVE:
				if(!changeMade) {
					tempInt1 = controls.axWaveshaping;
					tempInt2 = controls.ayWaveshaping;
				}
				if(presses & DLPRESS) {
					itemIndex = 0;
					redraw = 1;
				} else if(presses & DRPRESS) {
					itemIndex = 1;
					redraw = 1;
				} else if(presses & DUPRESS) {
					if(itemIndex == 0) {
						controls.axWaveshaping = fmin(controls.waveshapingMax, controls.axWaveshaping+1);
					} else {//itemIndex == 1
						controls.ayWaveshaping = fmin(controls.waveshapingMax, controls.ayWaveshaping+1);
					}
					changeMade = (controls.axWaveshaping != tempInt1) || (controls.ayWaveshaping != tempInt2);
					redraw = 1;
				} else if(presses & DDPRESS) {
					if(itemIndex == 0) {
						controls.axWaveshaping = fmax(controls.waveshapingMin, controls.axWaveshaping-1);
					} else {//itemIndex == 1
						controls.ayWaveshaping = fmax(controls.waveshapingMin, controls.ayWaveshaping-1);
					}
					changeMade = (controls.axWaveshaping != tempInt1) || (controls.ayWaveshaping != tempInt2);
					redraw = 1;
				} else if((presses & BSAVE) && changeMade) {
					setWaveshapingSetting(controls.axWaveshaping, ASTICK, XAXIS);
					setWaveshapingSetting(controls.ayWaveshaping, ASTICK, YAXIS);
					tempInt1 = controls.axWaveshaping;
					tempInt2 = controls.ayWaveshaping;
					changeMade = false;
					redraw = 1;
					pleaseCommit = 1;//ask the other thread to commit settings to flash
				}
				return;
			case MENU_ASMOOTH:
				if(!changeMade) {
					tempInt1 = controls.axSmoothing;
					tempInt2 = controls.aySmoothing;
				}
				if(presses & DLPRESS) {
					itemIndex = 0;
					redraw = 1;
				} else if(presses & DRPRESS) {
					itemIndex = 1;
					redraw = 1;
				} else if(presses & DUPRESS) {
					if(itemIndex == 0) {
						controls.axSmoothing = fmin(controls.smoothingMax, controls.axSmoothing+1);
					} else {//itemIndex == 1
						controls.aySmoothing = fmin(controls.smoothingMax, controls.aySmoothing+1);
					}
					changeMade = (controls.axSmoothing != tempInt1) || (controls.aySmoothing != tempInt2);
					redraw = 1;
				} else if(presses & DDPRESS) {
					if(itemIndex == 0) {
						controls.axSmoothing = fmax(controls.smoothingMin, controls.axSmoothing-1);
					} else {//itemIndex == 1
						controls.aySmoothing = fmax(controls.smoothingMin, controls.aySmoothing-1);
					}
					changeMade = (controls.axSmoothing != tempInt1) || (controls.aySmoothing != tempInt2);
					redraw = 1;
				} else if((presses & BSAVE) && changeMade) {
					setXSmoothingSetting(controls.axSmoothing);
					setYSmoothingSetting(controls.aySmoothing);
					tempInt1 = controls.axSmoothing;
					tempInt2 = controls.aySmoothing;
					changeMade = false;
					redraw = 1;
					pleaseCommit = 1;//ask the other thread to commit settings to flash
				}
				return;
			case MENU_CSNAPBACK:
				if(!changeMade) {
					tempInt1 = controls.cxSmoothing;
					tempInt2 = controls.cySmoothing;
				}
				if(presses & DLPRESS) {
					itemIndex = 0;
					redraw = 1;
				} else if(presses & DRPRESS) {
					itemIndex = 1;
					redraw = 1;
				} else if(presses & DUPRESS) {
					if(itemIndex == 0) {
						controls.cxSmoothing = fmin(controls.smoothingMax, controls.cxSmoothing+1);
					} else {//itemIndex == 1
						controls.cySmoothing = fmin(controls.smoothingMax, controls.cySmoothing+1);
					}
					changeMade = (controls.cxSmoothing != tempInt1) || (controls.cySmoothing != tempInt2);
					redraw = 1;
				} else if(presses & DDPRESS) {
					if(itemIndex == 0) {
						controls.cxSmoothing = fmax(controls.smoothingMin, controls.cxSmoothing-1);
					} else {//itemIndex == 1
						controls.cySmoothing = fmax(controls.smoothingMin, controls.cySmoothing-1);
					}
					changeMade = (controls.cxSmoothing != tempInt1) || (controls.cySmoothing != tempInt2);
					redraw = 1;
				} else if((presses & BSAVE) && changeMade) {
					setCxSmoothingSetting(controls.cxSmoothing);
					setCySmoothingSetting(controls.cySmoothing);
					tempInt1 = controls.cxSmoothing;
					tempInt2 = controls.cySmoothing;
					changeMade = false;
					redraw = 1;
					pleaseCommit = 1;//ask the other thread to commit settings to flash
				}
				return;
			case MENU_CWAVE:
				if(!changeMade) {
					tempInt1 = controls.cxWaveshaping;
					tempInt2 = controls.cyWaveshaping;
				}
				if(presses & DLPRESS) {
					itemIndex = 0;
					redraw = 1;
				} else if(presses & DRPRESS) {
					itemIndex = 1;
					redraw = 1;
				} else if(presses & DUPRESS) {
					if(itemIndex == 0) {
						controls.cxWaveshaping = fmin(controls.waveshapingMax, controls.cxWaveshaping+1);
					} else {//itemIndex == 1
						controls.cyWaveshaping = fmin(controls.waveshapingMax, controls.cyWaveshaping+1);
					}
					changeMade = (controls.cxWaveshaping != tempInt1) || (controls.cyWaveshaping != tempInt2);
					redraw = 1;
				} else if(presses & DDPRESS) {
					if(itemIndex == 0) {
						controls.cxWaveshaping = fmax(controls.waveshapingMin, controls.cxWaveshaping-1);
					} else {//itemIndex == 1
						controls.cyWaveshaping = fmax(controls.waveshapingMin, controls.cyWaveshaping-1);
					}
					changeMade = (controls.cxWaveshaping != tempInt1) || (controls.cyWaveshaping != tempInt2);
					redraw = 1;
				} else if((presses & BSAVE) && changeMade) {
					setWaveshapingSetting(controls.cxWaveshaping, CSTICK, XAXIS);
					setWaveshapingSetting(controls.cyWaveshaping, CSTICK, YAXIS);
					tempInt1 = controls.cxWaveshaping;
					tempInt2 = controls.cyWaveshaping;
					changeMade = false;
					redraw = 1;
					pleaseCommit = 1;//ask the other thread to commit settings to flash
				}
				return;
				/*
			case MENU_COFFSET:
				if(!changeMade) {
					tempInt1 = controls.cXOffset;
					tempInt2 = controls.cYOffset;
				}
				if(presses & DLPRESS) {
					itemIndex = 0;
					redraw = 1;
				} else if(presses & DRPRESS) {
					itemIndex = 1;
					redraw = 1;
				} else if(presses & DUPRESS) {
					if(itemIndex == 0) {
						controls.cXOffset = fmin(controls.cMax, controls.cXOffset+1);
					} else {//itemIndex == 1
						controls.cYOffset = fmin(controls.cMax, controls.cYOffset+1);
					}
					changeMade = (controls.cXOffset != tempInt1) || (controls.cYOffset != tempInt2);
					redraw = 1;
				} else if(presses & DDPRESS) {
					if(itemIndex == 0) {
						controls.cXOffset = fmax(controls.cMin, controls.cXOffset-1);
					} else {//itemIndex == 1
						controls.cYOffset = fmax(controls.cMin, controls.cYOffset-1);
					}
					changeMade = (controls.cXOffset != tempInt1) || (controls.cYOffset != tempInt2);
					redraw = 1;
				} else if((presses & BSAVE) && changeMade) {
					setCxOffsetSetting(controls.cXOffset);
					setCyOffsetSetting(controls.cYOffset);
					tempInt1 = controls.cXOffset;
					tempInt2 = controls.cYOffset;
					changeMade = false;
					redraw = 1;
					pleaseCommit = 1;//ask the other thread to commit settings to flash
				}
				return;
				*/
			case MENU_CARDINALS:
				if(!changeMade) {
					tempInt1 = controls.astickCardinalSnapping;
					tempInt2 = controls.cstickCardinalSnapping;
				}
				if(presses & DLPRESS) {
					itemIndex = 0;
					redraw = 1;
				} else if(presses & DRPRESS) {
					itemIndex = 1;
					redraw = 1;
				} else if(presses & DUPRESS) {
					if(itemIndex == 0) {
						controls.astickCardinalSnapping = fmin(controls.cardinalSnappingMax, controls.astickCardinalSnapping+1);
					} else {//itemIndex == 1
						controls.cstickCardinalSnapping = fmin(controls.cardinalSnappingMax, controls.cstickCardinalSnapping+1);
					}
					changeMade = (controls.astickCardinalSnapping != tempInt1) || (controls.cstickCardinalSnapping != tempInt2);
					redraw = 1;
				} else if(presses & DDPRESS) {
					if(itemIndex == 0) {
						controls.astickCardinalSnapping = fmax(controls.cardinalSnappingMin, controls.astickCardinalSnapping-1);
					} else {//itemIndex == 1
						controls.cstickCardinalSnapping = fmax(controls.cardinalSnappingMin, controls.cstickCardinalSnapping-1);
					}
					changeMade = (controls.astickCardinalSnapping != tempInt1) || (controls.cstickCardinalSnapping != tempInt2);
					redraw = 1;
				} else if((presses & BSAVE) && changeMade) {
					setCardinalSnappingSetting(controls.astickCardinalSnapping, ASTICK);
					setCardinalSnappingSetting(controls.cstickCardinalSnapping, CSTICK);
					tempInt1 = controls.astickCardinalSnapping;
					tempInt2 = controls.cstickCardinalSnapping;
					changeMade = false;
					redraw = 1;
					pleaseCommit = 1;//ask the other thread to commit settings to flash
				}
				return;
			case MENU_RADIUS:
				if(!changeMade) {
					tempInt1 = controls.astickAnalogScaler;
					tempInt2 = controls.cstickAnalogScaler;
				}
				if(presses & DLPRESS) {
					itemIndex = 0;
					redraw = 1;
				} else if(presses & DRPRESS) {
					itemIndex = 1;
					redraw = 1;
				} else if(presses & DUPRESS) {
					if(itemIndex == 0) {
						controls.astickAnalogScaler = fmin(controls.analogScalerMax, controls.astickAnalogScaler+1);
					} else {//itemIndex == 1
						controls.cstickAnalogScaler = fmin(controls.analogScalerMax, controls.cstickAnalogScaler+1);
					}
					changeMade = (controls.astickAnalogScaler != tempInt1) || (controls.cstickAnalogScaler != tempInt2);
					redraw = 1;
				} else if(presses & DDPRESS) {
					if(itemIndex == 0) {
						controls.astickAnalogScaler = fmax(controls.analogScalerMin, controls.astickAnalogScaler-1);
					} else {//itemIndex == 1
						controls.cstickAnalogScaler = fmax(controls.analogScalerMin, controls.cstickAnalogScaler-1);
					}
					changeMade = (controls.astickAnalogScaler != tempInt1) || (controls.cstickAnalogScaler != tempInt2);
					redraw = 1;
				} else if((presses & BSAVE) && changeMade) {
					setAnalogScalerSetting(controls.astickAnalogScaler, ASTICK);
					setAnalogScalerSetting(controls.cstickAnalogScaler, CSTICK);
					tempInt1 = controls.astickAnalogScaler;
					tempInt2 = controls.cstickAnalogScaler;
					changeMade = false;
					redraw = 1;
					pleaseCommit = 1;//ask the other thread to commit settings to flash
				}
				return;
			case MENU_REMAP:
				if((presses & SPRESS) && currentRemapStep == -1) {
					pleaseCommit = 10;
				}
				if((currentRemapStep > -1) && presses & (APRESS | BTAP | DUPRESS | LRPRESS | XPRESS | YPRESS | ZPRESS)) {
					pleaseCommit = 10;
				}
				return;
			case MENU_RUMBLE:
				if(!changeMade) {
					tempInt1 = controls.rumble;
				}
				if(presses & DUPRESS) {
					controls.rumble = fmin(controls.rumbleMax, controls.rumble+1);
					changeMade = controls.rumble != tempInt1;
					redraw = 1;
				} else if(presses & DDPRESS) {
					controls.rumble = fmax(controls.rumbleMin, controls.rumble-1);
					changeMade = controls.rumble != tempInt1;
					redraw = 1;
				} else if(presses & ZPRESS) {
					pleaseCommit = 8;//request rumble
				} else if((presses & BSAVE) && changeMade) {
					setRumbleSetting(controls.rumble);
					tempInt1 = controls.rumble;
					changeMade = false;
					redraw = 1;
					pleaseCommit = 1;//ask the other thread to commit settings to flash
				}
				return;
			case MENU_LTRIGGER:
				if(!changeMade) {
					tempInt1 = controls.lConfig;
					tempInt2 = controls.lTriggerOffset;
				}
				if(presses & DLPRESS) {
					itemIndex = 0;
					redraw = 1;
				} else if(presses & DRPRESS) {
					itemIndex = 1;
					redraw = 1;
				} else if(presses & DUPRESS) {
					if(itemIndex == 0) {
						controls.lConfig = fmin(controls.triggerConfigMax, controls.lConfig+1);
					} else {//itemIndex == 1
						controls.lTriggerOffset = fmin(controls.triggerMax, controls.lTriggerOffset+1);
					}
					changeMade = (controls.lConfig != tempInt1) || (controls.lTriggerOffset != tempInt2);
					redraw = 1;
				} else if(presses & DDPRESS) {
					if(itemIndex == 0) {
						controls.lConfig = fmax(controls.triggerConfigMin, controls.lConfig-1);
					} else {//itemIndex == 1
						controls.lTriggerOffset = fmax(controls.triggerMin, controls.lTriggerOffset-1);
					}
					changeMade = (controls.lConfig != tempInt1) || (controls.lTriggerOffset != tempInt2);
					redraw = 1;
				} else if((presses & BSAVE) && changeMade) {
					setLSetting(controls.lConfig);
					setLOffsetSetting(controls.lTriggerOffset);
					tempInt1 = controls.lConfig;
					tempInt2 = controls.lTriggerOffset;
					changeMade = false;
					redraw = 1;
					pleaseCommit = 1;//ask the other thread to commit settings to flash
				}
				return;
			case MENU_RTRIGGER:
				if(!changeMade) {
					tempInt1 = controls.rConfig;
					tempInt2 = controls.rTriggerOffset;
				}
				if(presses & DLPRESS) {
					itemIndex = 0;
					redraw = 1;
				} else if(presses & DRPRESS) {
					itemIndex = 1;
					redraw = 1;
				} else if(presses & DUPRESS) {
					if(itemIndex == 0) {
						controls.rConfig = fmin(controls.triggerConfigMax, controls.rConfig+1);
					} else {//itemIndex == 1
						controls.rTriggerOffset = fmin(controls.triggerMax, controls.rTriggerOffset+1);
					}
					changeMade = (controls.rConfig != tempInt1) || (controls.rTriggerOffset != tempInt2);
					redraw = 1;
				} else if(presses & DDPRESS) {
					if(itemIndex == 0) {
						controls.rConfig = fmax(controls.triggerConfigMin, controls.rConfig-1);
					} else {//itemIndex == 1
						controls.rTriggerOffset = fmax(controls.triggerMin, controls.rTriggerOffset-1);
					}
					changeMade = (controls.rConfig != tempInt1) || (controls.rTriggerOffset != tempInt2);
					redraw = 1;
				} else if((presses & BSAVE) && changeMade) {
					setRSetting(controls.rConfig);
					setROffsetSetting(controls.rTriggerOffset);
					tempInt1 = controls.rConfig;
					tempInt2 = controls.rTriggerOffset;
					changeMade = false;
					redraw = 1;
					pleaseCommit = 1;//ask the other thread to commit settings to flash
				}
				return;
			case MENU_TOURNEY:
				if(!changeMade) {
					tempInt1 = controls.tournamentToggle;
				}
				if(presses & DUPRESS) {
					controls.tournamentToggle = fmin(controls.tournamentToggleMax, controls.tournamentToggle+1);
					changeMade = controls.tournamentToggle != tempInt1;
					redraw = 1;
				} else if(presses & DDPRESS) {
					controls.tournamentToggle = fmax(controls.tournamentToggleMin, controls.tournamentToggle-1);
					changeMade = controls.tournamentToggle != tempInt1;
					redraw = 1;
				} else if((presses & BSAVE) && changeMade) {
					setTournamentToggleSetting(controls.tournamentToggle);
					tempInt1 = controls.tournamentToggle;
					changeMade = false;
					redraw = 1;
					pleaseCommit = 1;//ask the other thread to commit settings to flash
				}
				return;
			case MENU_RESET:
				if(presses & DUPRESS) {
					itemIndex = 0;
					redraw = 1;
				} else if(presses & DDPRESS) {
					itemIndex = 1;
					redraw = 1;
				} else if((presses & BSAVE) && itemIndex >= 2) {
					//if they briefly press B, back out
					itemIndex -= 2;
					redraw = 1;
				} else if((presses & APRESS) && itemIndex < 2) {
					//if they press A, go to the confirmation
					itemIndex += 2;
					redraw = 1;
				} else if((presses & APRESS) && itemIndex >= 2) {
					itemIndex -= 2;
					redraw = 1;
					if(itemIndex == 0) {
						//request a soft reset
						pleaseCommit = 2;
					} else {
						//request a hard reset
						pleaseCommit = 3;
					}
				}
				return;
			case MENU_XYSCOPE://stickmap plot
				if(!changeMade) {
					capture.stickThresh = 10;//fixed threshold for triggering
					tempInt1 = 0;//which stickmap to display
					capture.stickmap = 0;
					tempInt2 = 0;//left stick 0, c-stick 1
					capture.captureStick = ASTICK;
					tempInt3 = 0;//0 through 99
					capture.viewIndex = 0;
					changeMade = true;
				}
				if(presses & DUPRESS) {
					if(itemIndex != 0) {
						itemIndex--;
						redraw = 1;
					}
				} else if(presses & DDPRESS) {
					if(itemIndex < 2) {
						itemIndex++;
						redraw = 1;
					}
				} else if(presses & DLPRESS) {
					if(itemIndex == 0) {
						capture.stickmap = (capture.stickmap == 0) ? 0 : capture.stickmap-1;
					} else if(itemIndex == 1) {
						capture.captureStick = ASTICK;
					} else {
						capture.viewIndex = (capture.viewIndex == 0) ? 0 : capture.viewIndex-1;
					}
					redraw = 1;
				} else if(presses & DRPRESS) {
					if(itemIndex == 0) {
						capture.stickmap = fmin(6, capture.stickmap+1);
					} else if(itemIndex == 1) {
						capture.captureStick = CSTICK;
					} else {
						capture.viewIndex = fmin(99, capture.viewIndex+1);
					}
					redraw = 1;
				} else if(presses & SPRESS && capture.done == true) {
					//tell the user it's recording
					drawString(bitmap, 280, 250, 15, xyscope0);
					//set up recording
					capture.begin = false;
					capture.done = false;
					capture.mode = CM_STICK_RISE2;
					//then trigger the recording
					pleaseCommit = 9;
				}
				return;
			case MENU_TIMESCOPE://value vs time plot
				if(!changeMade) {
					capture.captureStick = ASTICK;//if triggers, then ASTICK is L, CSTICK is R
					capture.whichAxis = XAXIS;
					tempInt1 = 0;//capture stick + axis together, or triggers
					capture.mode = CM_STICK_FALL;//snapback (default)
					tempInt2 = 0;//snapback/dashback/pivot (only available for sticks)
					capture.viewIndex = 0;
					capture.autoRepeat = 1;//trigger automatically (except when itemIndex == 2)
					//clear data
					for(int i = 0; i<99; i++) {
						capture.a1[i] = (uint8_t) 0;
						capture.a2[i] = (uint8_t) 0;
						capture.a1Unfilt[i] = (uint8_t) 0;
						capture.a2Unfilt[i] = (uint8_t) 0;
						capture.abxyszrl[i] = (uint8_t) 0;
						capture.abxyszrl[i+100] = (uint8_t) 0;
					}
					changeMade = true;
				}
				if(presses & DLPRESS) {
					if(itemIndex != 0) {
						itemIndex--;
						capture.autoRepeat = 1;
						redraw = 1;
					}
				} else if(presses & DRPRESS) {
					if(itemIndex < 2) {
						itemIndex++;
						if(itemIndex == 2) {
							capture.autoRepeat = 0;
						} else {
							capture.autoRepeat = 1;
						}
						redraw = 1;
					}
				} else if(presses & DDPRESS) {
					if(itemIndex == 0) {
						tempInt1 = (tempInt1 == 0) ? 0 : tempInt1-1;
						switch(tempInt1) {
							case 0:
								capture.captureStick = ASTICK;
								capture.whichAxis = XAXIS;
								capture.mode = (tempInt2 == 0) ? CM_STICK_FALL : (tempInt2 == 1) ? CM_STICK_RISE : CM_STICK_PIVOT;
								break;
							case 1:
								capture.captureStick = ASTICK;
								capture.whichAxis = YAXIS;
								capture.mode = (tempInt2 == 0) ? CM_STICK_FALL : (tempInt2 == 1) ? CM_STICK_RISE : CM_STICK_PIVOT;
								break;
							case 2:
								capture.captureStick = CSTICK;
								capture.whichAxis = XAXIS;
								capture.mode = (tempInt2 == 0) ? CM_STICK_FALL : (tempInt2 == 1) ? CM_STICK_RISE : CM_STICK_PIVOT;
								break;
							case 3:
								capture.captureStick = CSTICK;
								capture.whichAxis = YAXIS;
								capture.mode = (tempInt2 == 0) ? CM_STICK_FALL : (tempInt2 == 1) ? CM_STICK_RISE : CM_STICK_PIVOT;
								break;
							case 4:
								capture.captureStick = ASTICK;
								capture.mode = CM_TRIG;
								break;
							case 5:
								capture.captureStick = CSTICK;
								capture.mode = CM_TRIG;
								break;
						}
						//every time we change capture params, we need to re-set-up recording just to be sure.
						//set up recording
						capture.begin = false;
						capture.triggered = false;
						capture.done = false;
						capture.startIndex = 0;
						capture.endIndex = 0;
						//then trigger the recording
						pleaseCommit = 9;
					} else if(itemIndex == 1) {
						if(tempInt1 < 4 && tempInt2 > 0) {//only applies when the sticks are selected
							tempInt2--;
							capture.mode = (tempInt2 == 0) ? CM_STICK_FALL : (tempInt2 == 1) ? CM_STICK_RISE : CM_STICK_PIVOT;
						}
						//every time we change capture params, we need to re-set-up recording just to be sure.
						//set up recording
						capture.begin = false;
						capture.triggered = false;
						capture.done = false;
						capture.startIndex = 0;
						capture.endIndex = 0;
						//then trigger the recording
						pleaseCommit = 9;
					} else {
						capture.viewIndex = (capture.viewIndex == 0) ? 0 : capture.viewIndex-1;
					}
					redraw = 1;
				} else if(presses & DUPRESS) {
					if(itemIndex == 0) {
						tempInt1 = fmin(5, tempInt1+1);
						switch(tempInt1) {
							case 0:
								capture.captureStick = ASTICK;
								capture.whichAxis = XAXIS;
								capture.mode = (tempInt2 == 0) ? CM_STICK_FALL : (tempInt2 == 1) ? CM_STICK_RISE : CM_STICK_PIVOT;
								break;
							case 1:
								capture.captureStick = ASTICK;
								capture.whichAxis = YAXIS;
								capture.mode = (tempInt2 == 0) ? CM_STICK_FALL : (tempInt2 == 1) ? CM_STICK_RISE : CM_STICK_PIVOT;
								break;
							case 2:
								capture.captureStick = CSTICK;
								capture.whichAxis = XAXIS;
								capture.mode = (tempInt2 == 0) ? CM_STICK_FALL : (tempInt2 == 1) ? CM_STICK_RISE : CM_STICK_PIVOT;
								break;
							case 3:
								capture.captureStick = CSTICK;
								capture.whichAxis = YAXIS;
								capture.mode = (tempInt2 == 0) ? CM_STICK_FALL : (tempInt2 == 1) ? CM_STICK_RISE : CM_STICK_PIVOT;
								break;
							case 4:
								capture.captureStick = ASTICK;
								capture.mode = CM_TRIG;
								break;
							case 5:
								capture.captureStick = CSTICK;
								capture.mode = CM_TRIG;
								break;
						}
						//every time we change capture params, we need to re-set-up recording just to be sure.
						//set up recording
						capture.begin = false;
						capture.triggered = false;
						capture.done = false;
						capture.startIndex = 0;
						capture.endIndex = 0;
						//then trigger the recording
						pleaseCommit = 9;
					} else if(itemIndex == 1) {
						if(tempInt1 < 4 && tempInt2 < 2) {//only applies when the sticks are selected
							tempInt2++;
							capture.mode = (tempInt2 == 0) ? CM_STICK_FALL : (tempInt2 == 1) ? CM_STICK_RISE : CM_STICK_PIVOT;
						}
						//every time we change capture params, we need to re-set-up recording just to be sure.
						//set up recording
						capture.begin = false;
						capture.triggered = false;
						capture.done = false;
						capture.startIndex = 0;
						capture.endIndex = 0;
						//then trigger the recording
						pleaseCommit = 9;
					} else {
						capture.viewIndex = fmin(199, capture.viewIndex+1);
					}
					redraw = 1;
				} else if(presses & SPRESS) {//this will be triggered by autorepeat
					//if we're framestepping, redraw the title
					if(itemIndex == 2) {
						eraseCharLine(bitmap, 20);
						drawString(bitmap,  20,  20, 15, MenuNames[menu]);
						drawString(bitmap, 240,  20, 15, xyscope0);
					}
					//set up recording
					capture.begin = false;
					capture.triggered = false;
					capture.done = false;
					capture.startIndex = 0;
					capture.endIndex = 0;
					//then trigger the recording
					pleaseCommit = 9;
				}
				return;
			case MENU_PRESSTIME:
				if(!changeMade) {
					capture.stickThresh = 23;//dash
					capture.triggerThresh = 255;//no lightshield threshold by default
					capture.autoRepeat = 1;//auto repeat by default
					changeMade = true;
				}
				if(presses & DLPRESS) {
					itemIndex = fmax(0, itemIndex-1);
					redraw = 1;
				} else if(presses & DRPRESS) {
					itemIndex = fmin(2, itemIndex+1);
					redraw = 1;
				} else if(presses & DUPRESS) {
					if(itemIndex == 0) {
						capture.stickThresh = fmin(100, capture.stickThresh+1);
					} else if(itemIndex == 1) {
						capture.triggerThresh = fmin(255, capture.triggerThresh+1);
					} else {//itemIndex == 2
						capture.autoRepeat = 1;
					}
					redraw = 1;
				} else if(presses & DDPRESS) {
					if(itemIndex == 0) {
						capture.stickThresh = fmax(10, capture.stickThresh-1);
					} else if(itemIndex == 1) {
						capture.triggerThresh = fmax(10, capture.triggerThresh-1);
					} else {//itemIndex == 2
						capture.autoRepeat = 0;
					}
					redraw = 1;
				} else if(presses & SPRESS) {//this will be triggered by autorepeat
					//tell the user to press ABXYLRZ or move a stick to begin
					drawString(bitmap, 30, 360, 15, presstime3);
					//set up recording
					capture.begin = false;
					capture.done = false;
					capture.endIndex = 0;
					capture.mode = CM_PRESS;
					//then trigger the recording
					pleaseCommit = 9;
				}
				return;
			case MENU_REACTION:
				if(!changeMade) {
					capture.stickThresh = 23;//dash
					capture.triggerThresh = 49;//lightshield
					changeMade = true;
				}
				if(presses & DLPRESS) {
					itemIndex = 0;
					redraw = 1;
				} else if(presses & DRPRESS) {
					itemIndex = 1;
					redraw = 1;
				} else if(presses & DUPRESS) {
					if(itemIndex == 0) {
						capture.stickThresh = fmin(100, capture.stickThresh+1);
					} else {//itemIndex == 1
						capture.triggerThresh = fmin(200, capture.triggerThresh+1);
					}
					redraw = 1;
				} else if(presses & DDPRESS) {
					if(itemIndex == 0) {
						capture.stickThresh = fmax(10, capture.stickThresh-1);
					} else {//itemIndex == 1
						capture.triggerThresh = fmax(10, capture.triggerThresh-1);
					}
					redraw = 1;
				} else if(presses & SPRESS) {
					//tell the user to get ready
					drawString(bitmap, 30, 150, 15, reaction8);
					//set up for recording the delay
					capture.delay = 0;
					capture.done = false;
					capture.mode = CM_NULL;
					//wait a random amount of time
					const uint32_t delay = rand() % 5'000'000 + 3'000'000; //3 to 8 seconds
					const uint32_t lastMicros = time_us_64();
					uint32_t thisMicros = lastMicros;
					while((thisMicros-lastMicros) < delay) {
						thisMicros = time_us_64();
					}
					//then trigger a redraw (which actually starts the recording)
					//(we want the recording to be synced to the redraw)
					pleaseCommit = 9;
					redraw = 1;
				}
				return;
			case MENU_PING:
				pleaseCommit = 100;//launch the game
				return;
			case MENU_VISION:
				if(!changeMade) {
					tempInt1 = controls.interlaceOffset;
				}
				if(presses & DUPRESS) {
					controls.interlaceOffset = fmin(controls.interlaceOffsetMax, controls.interlaceOffset+1);
					changeMade = controls.interlaceOffset != tempInt1;
					redraw = 1;
				} else if(presses & DDPRESS) {
					controls.interlaceOffset = fmax(controls.interlaceOffsetMin, controls.interlaceOffset-1);
					changeMade = controls.interlaceOffset != tempInt1;
					redraw = 1;
				} else if((presses & BSAVE) && changeMade) {
					setInterlaceOffsetSetting(controls.interlaceOffset);
					tempInt1 = controls.interlaceOffset;
					changeMade = false;
					redraw = 1;
					pleaseCommit = 1;//ask the other thread to commit settings to flash
				}
				return;
			default:
				//do nothing
				return;
		}
	}
}
