PhobGCC/PhobGCC-SW/PhobGCC/rp2040/src/cvideo.cpp

/*-----------------------------------------------
 * Pico-Composite8      Composite Video, 8-bit output
 *
 * 2021-06-04           obstruse@earthlink.net
 *-----------------------------------------------
*/

/* Based on:
 *-----------------------------------------------
 * Title:               Pico-mposite Video Output
 *  Author:             Dean Belfield
 *  Created:            26/01/2021
 *  Last Updated:       15/02/2021
 *-----------------------------------------------
*/
/*
    Copyright (C) 2021 Bill Neisius <obstruse@earthlink.net>

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
    You should have received a copy of the GNU General Public License
    along with this program.  If not, see <https://www.gnu.org/licenses/>.
*/

/* Modified to 4 bit depth a la https://github.com/obstruse/life */

#define TESTPATTERN

#include <stdlib.h>
#include <charconv>
//#include <stdio.h>
#include <string>
#include <cmath>
#include "memory.h"

#include "pico/stdlib.h"
#include "pico/multicore.h"
#include "pico.h"

#include "hardware/pio.h"
#include "hardware/dma.h"
#include "hardware/irq.h"

void cvideo_configure_pio_dma(PIO pio, uint sm, uint dma_channel, size_t buffer_size_words);
void cvideo_dma_handler(void);

#include "cvideo.pio.h"     // The assembled PIO code
#include "cvideo.h"
#include "cvideo_variables.h"
#include "games/ping.h"


/*-------------------------------------------------------------------*/
/*------------------Video Standard-----------------------------------*/
/*-------------------------------------------------------------------*/

const int   VIDEO_frame_lines = 525;
const int   VIDEO_frame_lines_visible = 480;
const float VIDEO_aspect_ratio = 4.0/3.0;
//const float VIDEO_horizontal_freq = 15750.0;
const float VIDEO_horizontal_freq = 15734.0;// 1000/1001 of the above
const float VIDEO_h_FP_usec = 1.5;	// front porch
const float VIDEO_h_SYNC_usec = 4.7;	// sync
const float VIDEO_h_BP_usec = 4.7;	// back porch
const float VIDEO_h_EP_usec = 2.3;	// equalizing pulse

/*-------------------------------------------------------------------*/
/*------------------Horizontal Derived-------------------------------*/
/*-------------------------------------------------------------------*/

const int   HORIZ_visible_dots = VIDEO_frame_lines_visible * VIDEO_aspect_ratio;	// full frame width; 480
const float HORIZ_usec = 1000000.0 / VIDEO_horizontal_freq;
const float HORIZ_usec_dot = (HORIZ_usec - VIDEO_h_FP_usec - VIDEO_h_SYNC_usec - VIDEO_h_BP_usec) / HORIZ_visible_dots;
const int   HORIZ_dots = HORIZ_usec / HORIZ_usec_dot; // 644

const int   HORIZ_bytes = HORIZ_dots / 2; // two dots per byte; 322
const int   HORIZ_FP_bytes = VIDEO_h_FP_usec / HORIZ_usec_dot / 2;
const int   HORIZ_SYNC_bytes = VIDEO_h_SYNC_usec / HORIZ_usec_dot / 2;
const int   HORIZ_BP_bytes = VIDEO_h_BP_usec / HORIZ_usec_dot / 2;
const int   HORIZ_EP_bytes = VIDEO_h_EP_usec / HORIZ_usec_dot / 2;	// equalizing pulse during vertical sync
const int   HORIZ_pixel_start = ((HORIZ_visible_dots - VWIDTH) / 2) / 2 + HORIZ_SYNC_bytes + HORIZ_BP_bytes;

/*-------------------------------------------------------------------*/
/*------------------Vertical Derived---------------------------------*/
/*-------------------------------------------------------------------*/

const int   VERT_scanlines = VIDEO_frame_lines / 2;				// one field
const int   VERT_vblank    = (VIDEO_frame_lines - VIDEO_frame_lines_visible) / 2;	// vertical blanking, one field
const int   VERT_border    = (VERT_scanlines - VERT_vblank - VHEIGHT/2) / 2;
const int   VERT_bitmap    = VHEIGHT/2;

/*-------------------------------------------------------------------*/
/*------------------PIO----------------------------------------------*/
/*-------------------------------------------------------------------*/

const float PIO_clkdot = 1.0;        	// PIO instructions per dot
//const float PIO_sysclk = 125000000.0;	// default Pico system clock
const float PIO_sysclk = 250000000.0;	// default Pico system clock
const float PIO_clkdiv = PIO_sysclk / VIDEO_horizontal_freq / PIO_clkdot / HORIZ_dots;

#define state_machine 0     // The PIO state machine to use
uint dma_channel;           // DMA channel for transferring hsync data to PIO

uint vline = 9999;          // Current video line being processed
uint bline = 0;             // Line in the bitmap to fetch
uint field = 0;		        // field, even/odd

int bmIndex = 0;
int bmCount = 0;

// bitmap buffer
unsigned char _bitmap[BUFFERLEN];

unsigned char * vsync_ll;                             // buffer for a vsync line with a long/long pulse
unsigned char * vsync_ss;                             // Buffer for an equalizing line with a short/short pulse
unsigned char * vsync_bb;                             // Buffer for a vsync blanking
unsigned char * vsync_ssb;                            // Buffer and a half for equalizing/blank line
unsigned char * border;                               // Buffer for a vsync line for the top and bottom borders
unsigned char * pixel_buffer[2];                      // Double-buffer for the pixel data scanlines

volatile bool _changeBitmap = false;
volatile bool _startSync = false;
volatile int _frameCount = 0;

volatile int _interlaceOffset = 0;

/*-------------------------------------------------------------------*/
int videoOut(const uint8_t pin_base,
		Buttons &btn,
		Buttons &hardware,
		RawStick &raw,
		ControlConfig &config,
		StickParams &aStick,
		StickParams &cStick,
		DataCapture &capture,
		volatile bool &extSync,
		volatile uint8_t &pleaseCommit,
		int &currentCalStep,
		int &currentRemapStep,
		const int version) {

	_interlaceOffset = config.interlaceOffset;

	memset(_bitmap, BLACK2, BUFFERLEN);

	vsync_ll = (unsigned char *)malloc(HORIZ_bytes);
	memset(vsync_ll, SYNC, HORIZ_bytes);				// vertical sync/serrations
	memset(vsync_ll + (HORIZ_bytes>>1) - HORIZ_EP_bytes, BLANK2, HORIZ_EP_bytes);
	memset(vsync_ll + HORIZ_bytes      - HORIZ_EP_bytes, BLANK2, HORIZ_EP_bytes);

	vsync_ss = (unsigned char *)malloc(HORIZ_bytes);
	memset(vsync_ss, BLANK2, HORIZ_bytes);				// vertical equalizing
	memset(vsync_ss, SYNC, HORIZ_EP_bytes);
	memset(vsync_ss + (HORIZ_bytes>>1), SYNC, HORIZ_EP_bytes);

	vsync_bb = (unsigned char *)malloc(HORIZ_bytes);
	memset(vsync_bb, BLANK2, HORIZ_bytes);				// vertical blanking
	memset(vsync_bb, SYNC, HORIZ_SYNC_bytes);

	vsync_ssb = (unsigned char *)malloc(HORIZ_bytes+HORIZ_bytes);
	memset(vsync_ssb, BLANK2, HORIZ_bytes + HORIZ_bytes);		// vertical equalizing/blanking
	memset(vsync_ssb, SYNC, HORIZ_EP_bytes);
	memset(vsync_ssb + (HORIZ_bytes>>1), SYNC, HORIZ_EP_bytes);

	// This bit pre-builds the border scanline and pixel buffers
	border = (unsigned char *)malloc(HORIZ_bytes);
	memset(border, GRAY2, HORIZ_bytes);			// Fill the border with the border colour
	memset(border, SYNC, HORIZ_SYNC_bytes);		        // Add the hsync pulse
	memset(border + HORIZ_SYNC_bytes,             BLANK2, HORIZ_BP_bytes);
	memset(border + HORIZ_bytes - HORIZ_FP_bytes, BLANK2, HORIZ_FP_bytes);		// front porch

	pixel_buffer[0] = (unsigned char *)malloc(HORIZ_bytes);
	memcpy(pixel_buffer[0], border, HORIZ_bytes);			// pixel buffer
	pixel_buffer[1] = (unsigned char *)malloc(HORIZ_bytes);
	memcpy(pixel_buffer[1], border, HORIZ_bytes);			// pixel buffer

	// Initialise the PIO
	PIO pio = pio0;
	uint offset = pio_add_program(pio, &cvideo_program);	// Load up the PIO program
	pio_sm_set_enabled(pio, state_machine, false);          // Disable the PIO state machine
	pio_sm_clear_fifos(pio, state_machine);	                // Clear the PIO FIFO buffers
	cvideo_initialise_pio(pio, state_machine, offset, pin_base, 4, PIO_clkdiv); // Initialise the PIO (function in cvideo.pio)

	dma_channel = dma_claim_unused_channel(true);		    // Claim a DMA channel for the hsync transfer
	cvideo_configure_pio_dma(pio, state_machine, dma_channel, HORIZ_bytes); // Hook up the DMA channel to the state machine

	// And kick everything off
	cvideo_dma_handler();
	pio_sm_set_enabled(pio, state_machine, true);           // Enable the PIO state machine

	unsigned int menuIndex = 0;;
	int itemIndex = 0;;
	uint8_t redraw = 1;//start off with a normal redraw
	bool changeMade = false;

	while (true) {
		//tight_loop_contents();
		while(!_startSync) {
			tight_loop_contents();
		}
		extSync = true;
		_startSync = false;

		if(pleaseCommit == 255) {
			//this is a signal from the other side to redraw after variables have changed
			redraw = 1;
			pleaseCommit = 0;
		}

		//run games
		if(pleaseCommit == 100) {
			if(runPing(_bitmap, hardware, raw, config)) {
				pleaseCommit = 99;//go back from the game
			}
		}

		//handle normal menus
		if(pleaseCommit < 100) {
			handleMenuButtons(_bitmap, menuIndex, itemIndex, redraw, changeMade, currentCalStep, currentRemapStep, pleaseCommit, btn, hardware, config, capture);

			if(redraw == 2) { //fast redraw
				redraw = 0;
				drawMenuFast(_bitmap, menuIndex, itemIndex, changeMade, currentCalStep, currentRemapStep, btn, hardware, raw, config, aStick, cStick);
			} else if(redraw == 1) { //slow redraw
				redraw = 0;
				//write interlace offset
				_interlaceOffset = config.interlaceOffset;
				memset(_bitmap, BLACK2, BUFFERLEN);
				drawMenu(_bitmap, menuIndex, itemIndex, changeMade, currentCalStep, currentRemapStep, version, btn, raw, config, aStick, cStick, capture);
			}
		}
	}
}

/*-------------------------------------------------------------------*/
// The DMA interrupt handler
// This is triggered by DMA_IRQ_0

void __no_inline_not_in_flash_func(cvideo_dma_handler)(void) {

	if ( ++vline <= VERT_scanlines ) {
	} else {
		vline = 0;
		bline = 0;
		field = ++field & 0x01;
		//_frameCount++;
	}

    while (true) {
		if ( vline <= VERT_vblank ) {
			switch(vline) {
				case 0:
					// for some reason interlace fails unless there's a 30usec delay here:
					//busy_wait_us(HORIZ_usec/2);
					//busy_wait_us(HORIZ_usec/4);
					//actually, for phobvision it seems to work best with no delay
					//with the delay, the adc reads make it twitch for some reason
					//interlacing works fine without it too, if not better without
					if ( !field ) {
						// odd field - blank, full line
						dma_channel_set_read_addr(dma_channel, vsync_bb, true);
			        } else {
						// even field - blank, half line
						dma_channel_set_trans_count(dma_channel, HORIZ_bytes/2 + _interlaceOffset, false);
						dma_channel_set_read_addr(dma_channel, vsync_bb, true);
			        }
					break;
			    case 1:
					dma_channel_set_trans_count(dma_channel, HORIZ_bytes, false);   // reset transfer size
			    case 2 ... 3:
					// send 3 vsync_ss - 'equalizing pulses'
					dma_channel_set_read_addr(dma_channel, vsync_ss, true);
					break;
				case 4 ... 6:
					// send 3 vsync_ll - 'vertical sync/serrations'
					dma_channel_set_read_addr(dma_channel, vsync_ll, true);
					break;
				case 7 ... 8:
					// send 3 vsync_ss - 'equalizing pulses'
					dma_channel_set_read_addr(dma_channel, vsync_ss, true);
					break;
				case 9:
					if ( !field ) {
						// odd field - equalizing pulse, full line
						dma_channel_set_read_addr(dma_channel, vsync_ss, true);
					} else {
						//even field - equalizing pulse, line and a half
						dma_channel_set_trans_count(dma_channel, HORIZ_bytes + HORIZ_bytes/2 - _interlaceOffset, false);
						dma_channel_set_read_addr(dma_channel, vsync_ssb, true);
					}
					break;
		    	case 10:
					// everything back to normal
					dma_channel_set_trans_count(dma_channel, HORIZ_bytes, false);   // reset transfer size
				default:
					// send BLANK till end of vertical blanking
					dma_channel_set_read_addr(dma_channel, vsync_bb, true);
					break;
			}
			break;
		}
		if ( vline <= VERT_vblank + VERT_border ) {
			if (_changeBitmap) {
				dma_channel_set_read_addr(dma_channel, vsync_bb, true);
			} else {
				dma_channel_set_read_addr(dma_channel, border, true);
				if ( vline == VERT_vblank + VERT_border ) {
					memcpy(pixel_buffer[bline & 1] + HORIZ_pixel_start, _bitmap + (bline*2+field)*VWIDTH/2, VWIDTH/2);
				}
			}
			break;
		}
		if ( vline <= VERT_vblank + VERT_border + VERT_bitmap  ) {
			if (_changeBitmap) {
				dma_channel_set_read_addr(dma_channel, vsync_bb, true);
			} else {
				dma_channel_set_read_addr(dma_channel, pixel_buffer[bline++ & 1], true);    // Set the DMA to read from one of the pixel_buffers
				memcpy(pixel_buffer[bline & 1] + HORIZ_pixel_start, _bitmap + (bline*2+field)*VWIDTH/2, VWIDTH/2);       // And memcpy the next scanline
			}
			break;
		}
		// otherwise, just output border until end of scanlines
		//also, increment frame count
		if (vline == VERT_vblank + VERT_border + VERT_bitmap + 1) {
			_frameCount++;
		}
		if (_changeBitmap) {
			dma_channel_set_read_addr(dma_channel, vsync_bb, true);
		} else {
			dma_channel_set_read_addr(dma_channel, border, true);
		}
		break;
	}

	//sync to after the DMA
	if(_frameCount == 1) {
		_frameCount = 0;
		_startSync = true;
	}

	// Finally, clear the interrupt request ready for the next horizontal sync interrupt
	dma_hw->ints0 = 1u << dma_channel;
}

/*-------------------------------------------------------------------*/
// Configure the PIO DMA
// Parameters:
// - pio: The PIO to attach this to
// - sm: The state machine number
// - dma_channel: The DMA channel
// - buffer_size_words: Number of bytes to transfer
//
void cvideo_configure_pio_dma(PIO pio, uint sm, uint dma_channel, size_t buffer_size_words) {
	pio_sm_clear_fifos(pio, sm);
	dma_channel_config c = dma_channel_get_default_config(dma_channel);
	channel_config_set_transfer_data_size(&c, DMA_SIZE_8);
	channel_config_set_read_increment(&c, true);
	channel_config_set_dreq(&c, pio_get_dreq(pio, sm, true));

	dma_channel_configure(dma_channel, &c,
	                      &pio->txf[sm],              // Destination - PIO queue
	                      vsync_bb,                   // Source - Equalizing Pulses
	                      buffer_size_words,          // Number of transfers
	                      true                        // Start - queue the Source to the Destination
	                     );

	dma_channel_set_irq0_enabled(dma_channel, true);

	irq_set_exclusive_handler(DMA_IRQ_0, cvideo_dma_handler);
	irq_set_enabled(DMA_IRQ_0, true);
}
