PhobGCC/PhobGCC-SW/PhobGCC/rp2040/include/cvideo.h

#ifndef CVIDEO_H
#define CVIDEO_H

#include "structsAndEnums.h"

#ifndef VWIDTH
#define VWIDTH 512
#endif
#ifndef VWIDTHBYTE
#define VWIDTHBYTE 256
#endif
#ifndef VHEIGHT
#define VHEIGHT 384
#endif
#ifndef BUFFERLEN
#define BUFFERLEN 98304//512*384/2
#endif

enum LineOrPoint {
	LINEGRAPH,
	POINTGRAPH
};

int videoOut(const uint8_t pin_base,
		Buttons &btn,
		Buttons &hardware,
		RawStick &raw,
		ControlConfig &config,
		StickParams &aStick,
		StickParams &cStick,
		DataCapture &capture,
		volatile bool &extSync,
		volatile uint8_t &pleaseCommit,
		int &currentCalStep,
		int &currentRemapStep,
		const int version);

uint16_t getImageWidth(const unsigned char image[]);
uint16_t getImageHeight(const unsigned char image[]);
void drawImage(unsigned char bitmap[],
               const unsigned char image[],
               const unsigned char index[],
               const uint16_t x,
               const uint16_t y);

void drawLine(unsigned char bitmap[],
              const uint16_t xStart,
              const uint16_t yStart,
              const uint16_t xEnd,
              const uint16_t yEnd,
              const uint8_t color);

void drawString(unsigned char bitmap[],
                const uint16_t x,
                const uint16_t y,
                const uint8_t color,
                const char string[],
                const uint8_t charLimit = 99);

void drawString2x(unsigned char bitmap[],
                  const uint16_t x,
                  const uint16_t y,
                  const uint8_t color,
                  const char string[],
                  const uint8_t charLimit = 99);

void graphStickmap(unsigned char bitmap[],
                   const uint16_t x0,
                   const uint16_t y0,
                   const int x[],
                   const int y[],
                   const uint16_t length,
                   const uint8_t color,
                   const LineOrPoint graphType);

//drawFloat and drawInt draw numbers to the screen
//they handle negative numbers so that they don't misalign
//largestPower aligns the decimal point for numbers up to that power of ten;
// for example, largestPower=1 aligns numbers up to 2 digits to the left of the decimal
//For floats, totalChars only writes up to that number of characters.
// It truncates instead of rounding.
// Only does something if it's at least largestPower+2, which should only show whole numbers and the negative sign
// largestPower+3 makes it stop after writing the decimal point.
//0123456789
//-x.y for largestPower 0
//-xx.y for largestPower 1
//-xxx.y for largestPower 2
void drawFloat(unsigned char bitmap[],
               const uint16_t x0,
               const uint16_t y0,
               const uint8_t color,
               const uint8_t largestPower,
               const uint8_t totalChars,
               const float number);
void drawFloat2x(unsigned char bitmap[],
                 const uint16_t x0,
                 const uint16_t y0,
                 const uint8_t color,
                 const uint8_t largestPower,
                 const uint8_t totalChars,
                 const float number);
void drawInt(unsigned char bitmap[],
             const uint16_t x0,
             const uint16_t y0,
             const uint8_t color,
             const uint8_t largestPower,
             const int number);
void drawInt2x(unsigned char bitmap[],
               const uint16_t x0,
               const uint16_t y0,
               const uint8_t color,
               const uint8_t largestPower,
               const int number);

void drawMenuFast(unsigned char bitmap[],
                  const unsigned int menu,
                  const int itemIndex,
			      const bool changeMade,
                  const int currentCalStep,
				  const int currentRemapStep,
                  const Buttons btn,
                  const Buttons hardware,
                  const RawStick raw,
                  const ControlConfig &controls,
			      const StickParams &aStick,
			      const StickParams &cStick);

void drawMenu(unsigned char bitmap[],
              const unsigned int menu,
              const int itemIndex,
			  const bool changeMade,
			  const int currentCalStep,
			  const int currentRemapStep,
			  const int version,
              const Buttons btn,
              const RawStick raw,
              const ControlConfig &controls,
			  const StickParams &aStick,
			  const StickParams &cStick,
              DataCapture &capture);

void handleMenuButtons(unsigned char bitmap[],
                       unsigned int &menu,
                       int &itemIndex,
                       uint8_t &redraw,
				       bool &changeMade,
                       const int currentCalStep,
					   const int currentRemapStep,
				       volatile uint8_t &pleaseCommit,//for asking the other core to commit settings
					   const Buttons &btn,
                       const Buttons &hardware,
                       ControlConfig &controls,
					   DataCapture &capture);

void eraseCharLine(unsigned char bitmap[],
                    uint16_t y0);

void eraseRows(unsigned char bitmap[],
               uint16_t y0,
               uint16_t rows);

#endif //CVIDEO_H
