PhobGCC/PhobGCC-SW/PhobGCC/common/variables.h

#ifndef VARIABLES_H
#define VARIABLES_H

#include "structsAndEnums.h"


Buttons _btn;

Buttons _hardware;

RawStick _raw;

StickParams _aStickParams;

StickParams _cStickParams;

//ADC reference values for Phob 1.0
float _ADCScale = 1;
float _ADCScaleFactor = 1;

int _rumblePower = 0;

float _dT;

#endif //VARIABLES_H
